letfritz/COVID-ventilator/main/teste.c

#include <avr/io.h>
#include "globals_aux.h"

/*
extern uint16_t adc_value0;
extern uint16_t adc_value1;
extern uint16_t adc_value2;
extern uint16_t adc_value3;
extern uint16_t adc_value4;
extern uint16_t cont;
*/

void func_teste(void){
    cont++;
}
